BoujeeEnjinia1701/cellguard/cad/drawings/CGD-DWG-104.pdf

### BUILD PLAN SKETCH, PLAN NOT YET BUILT CellGuard · github.com/BoujeeEnjinia1701/cellguard

FRONT VIEW
Scale 1:2; looking at the front (along +Y)

TOP VIEW
Scale 1:2; looking down (along -Z)

RIGHT VIEW
Scale 1:2; looking at the right side (along -X)

134

104 26

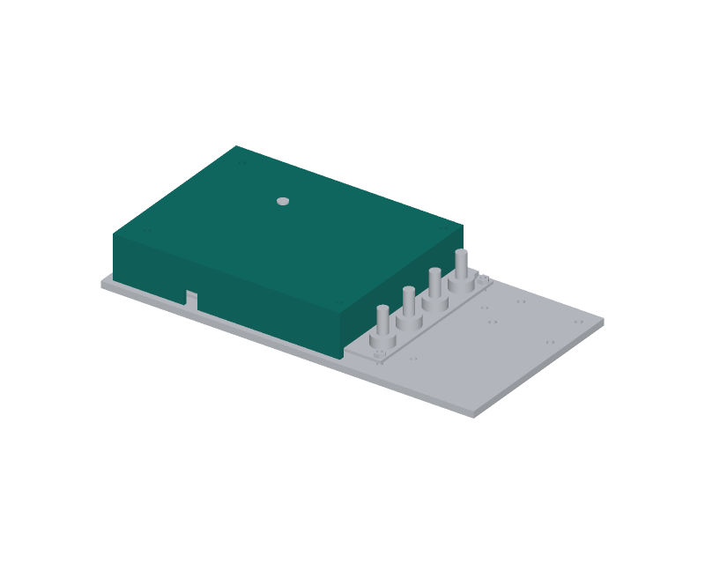
[picture p10: figure]

WHERE IT GOES
This part in colour, its neighbours in grey

HOW TO MAKE IT AND HOW IT FITS
Print upside down (top face on the bed), 2 mm walls, 100 % infill, in flame-retardant polycarbonate in an enclosed printer. Outside 134 x 104 x 26.1 mm, open at the bottom.
Four 3.4 mm holes in the top over the pillars: 12 mm from the signal end 40 each side, and 128 mm from it 44 each side. Signal-end notch 68 wide, from 26 below to 42 above the centre line, open at the bottom, 15.1 mm tall: the connectors and harness sit in it. Power-end notch 98 wide, 5.1 mm tall, open at the bottom: the board passes under it with 1 mm clear. Probe notch 8 wide, 9.1 mm tall, in the near side wall.
Light pipe hole 3.2 mm in the top, 50 mm from the signal end, 20 to the B+ side: press the flanged 3 mm light pipe in from above; its foot stops 0.5 mm over the status light.
Fit: it rests on the four pillars only; its walls stand 0.5 mm clear of the plate. Four M3 x 6 pan-head screws.
Check: on the pillars it does not rock and touches no part.
REV | DESCRIPTION | DATE | BY
P1 | Making sketch for the prototype build plan | 2026-09-30 | AC
P2 | Status light and light pipe added (CGD-DEC-001) | 2026-10-02 | AC
CELLGUARD | github.com/BoujeeEnjinia1701/cellguard

## CellGuard cover: making sketch

DRAWING NO.
CGD-DWG-104

REV
P2

SHEET
1 of 1

SIZE

## ANSI B

SCALE
1:2

UNITS
mm
PROJECTION | DATE
2026-10-02

DRAWN
Amish Chadha

MATERIAL / NOTES
Flame-retardant polycarbonate, opaque, printed, 2 mm wall
Licensed CERN-OHL-S-2.0 · Design Molecule Lab · designmolecule.com | Generated from cad/src; do not edit by hand
