BoujeeEnjinia1701/cellguard/cad/drawings/CGD-DWG-101.pdf

### BUILD PLAN SKETCH, PLAN NOT YET BUILT CellGuard · github.com/BoujeeEnjinia1701/cellguard

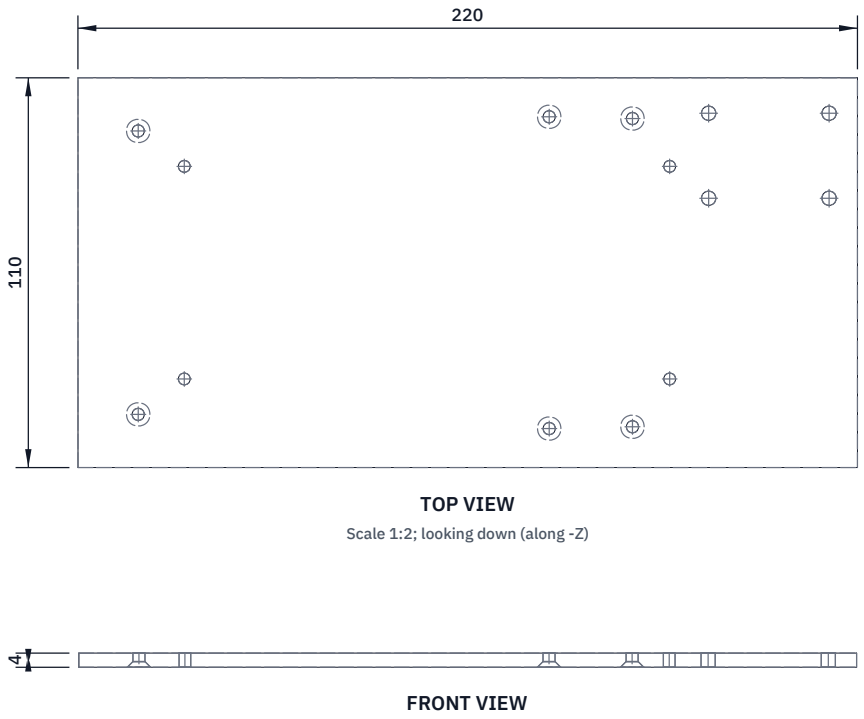
[picture p36: figure]
FRONT VIEW; TOP VIEW; Scale 1:2; looking down (along -Z)

Scale 1:2; looking at the front (along +Y)

RIGHT VIEW
Scale 1:2; looking at the right side (along -X)

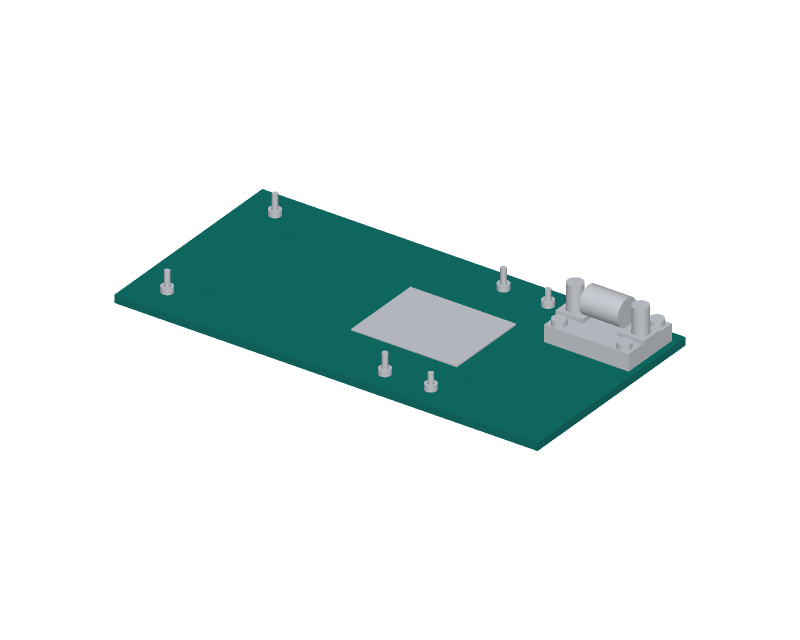
[picture p37: figure]

WHERE IT GOES
This part in colour, its neighbours in grey

HOW TO MAKE IT AND HOW IT FITS
Blank 220 x 110 mm, 4 mm aluminium, square; round the corners 3 mm. Sizes from the signal end (left edge) and the centre line.
Board fixings: six 3.4 mm holes, countersunk 90 degrees from
the BOTTOM face to 6.6 mm so M3 countersunk heads sit flush:
17 from the left edge 40 each side; 133 in, 44 each side;
156.5 in, 43.5 each side.
Fuse holder: four M4 tapped holes (drill 3.3) at 178 and 212 in, 21 and 45 to the B+ side of the centre line.
Mounting: four M4 tapped holes (drill 3.3) at 30 and 167 in,
30 each side. Screws come up from below and stop in the plate. Deburr every hole; the top face must stay flat within 0.1 mm under the gap pad (it carries the MOSFET heat).
Check: lay the board on it; all six holes line up with the board's.
REV | DESCRIPTION | DATE | BY
P1 | Making sketch for the prototype build plan | 2026-09-30 | AC
CELLGUARD | github.com/BoujeeEnjinia1701/cellguard

## CellGuard base plate: making sketch

DRAWING NO.
CGD-DWG-101

REV
P1

SHEET
1 of 1

SIZE

## ANSI B

SCALE
1:2

UNITS
mm
PROJECTION | DATE
2026-09-30

DRAWN
Amish Chadha

MATERIAL / NOTES
Aluminium sheet 4 mm, 6061 class
Licensed CERN-OHL-S-2.0 · Design Molecule Lab · designmolecule.com | Generated from cad/src; do not edit by hand
