BoujeeEnjinia1701/cellguard/cad/drawings/CGD-DWG-102.pdf

### BUILD PLAN SKETCH, PLAN NOT YET BUILT CellGuard · github.com/BoujeeEnjinia1701/cellguard

FRONT VIEW
Scale 2:1; looking at the front (along +Y)

TOP VIEW
Scale 2:1; looking down (along -Z)

RIGHT VIEW
Scale 2:1; looking at the right side (along -X)

55

44 1

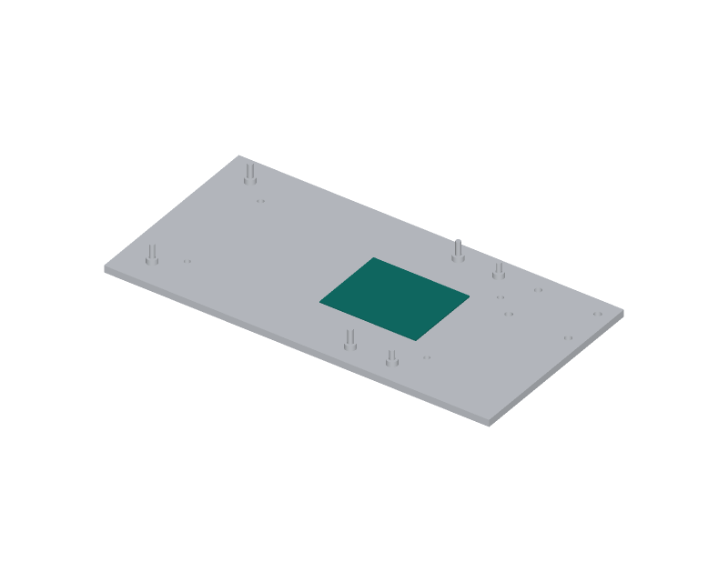
[picture p38: figure]

WHERE IT GOES
This part in colour, its neighbours in grey

HOW TO MAKE IT AND HOW IT FITS
Cut one piece 55 x 44 mm from 1.0 mm insulating gap pad sheet with a sharp knife on a cutting mat; keep the liner on.
Drawn at 0.7 mm: the thickness it is squeezed to in place.
It lies on the plate under the eight MOSFETs: from 100 to 155 mm in from the plate's left edge, centred across the plate.
Peel one liner, press it onto the clean plate, then peel the
other liner just before the board goes on.
Do not stretch it; replace it if it tears or picks up a chip:
it is the only insulation between the MOSFETs and the plate. Check: no bubbles; 55 x 44 mm within 1 mm.
REV | DESCRIPTION | DATE | BY
P1 | Making sketch for the prototype build plan | 2026-09-30 | AC
CELLGUARD | github.com/BoujeeEnjinia1701/cellguard

## CellGuard gap pad: cutting sketch

DRAWING NO.
CGD-DWG-102

REV
P1

SHEET
1 of 1

SIZE

## ANSI B

SCALE
2:1

UNITS
mm
PROJECTION | DATE
2026-09-30

DRAWN
Amish Chadha

MATERIAL / NOTES
Insulating gap pad 1.0 mm, 3 W/m.K
Licensed CERN-OHL-S-2.0 · Design Molecule Lab · designmolecule.com | Generated from cad/src; do not edit by hand
