BoujeeEnjinia1701/cellguard/cad/drawings/CGD-DWG-105.pdf

### BUILD PLAN SKETCH, PLAN NOT YET BUILT CellGuard · github.com/BoujeeEnjinia1701/cellguard

FRONT VIEW
Scale 2:1; looking at the front (along +Y)

TOP VIEW
Scale 2:1; looking down (along -Z)

RIGHT VIEW
Scale 2:1; looking at the right side (along -X)

41

14 3

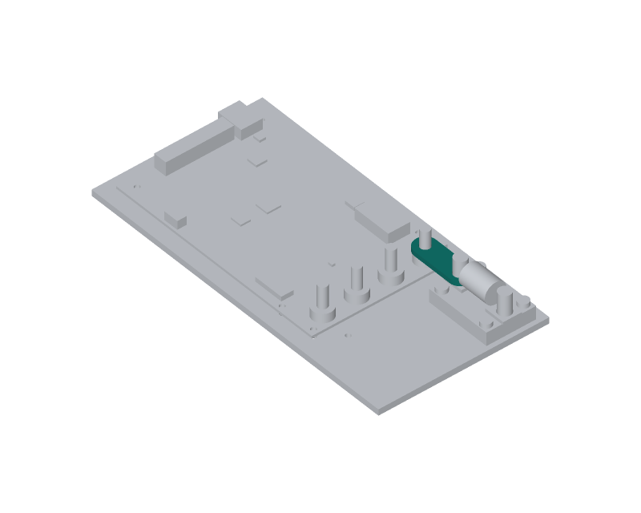
[picture p39: figure]

WHERE IT GOES
This part in colour, its neighbours in grey

HOW TO MAKE IT AND HOW IT FITS
Cut 41 mm of 14 x 3 mm copper bar; file both ends to a 7 mm radius, centred on the hole centres.
Holes on the centre line, 27 mm apart: 6.5 mm at one end (B+ stud, M6), 8.5 mm at the other (fuse holder terminal, M8). Deburr; clean both faces bright with an abrasive pad.
Slide 20 mm of heat-shrink over the middle and shrink it; leave the ends bare where they clamp.
Fit: lies flat on the B+ stud's shoulder and on the fuse blade
at the holder's inner terminal, both 10.6 mm above the plate top. An M6 and an M8 nut with spring washers hold it.
It carries the full pack current: both faces must be clean and flat where they touch.
Check: drops over both studs without bending.
REV | DESCRIPTION | DATE | BY
P1 | Making sketch for the prototype build plan | 2026-09-30 | AC
CELLGUARD | github.com/BoujeeEnjinia1701/cellguard

## CellGuard fuse link: making sketch

DRAWING NO.
CGD-DWG-105

REV
P1

SHEET
1 of 1

SIZE

## ANSI B

SCALE
2:1

UNITS
mm
PROJECTION | DATE
2026-09-30

DRAWN
Amish Chadha

MATERIAL / NOTES
Copper flat bar 14 x 3 mm, C101 or C110
Licensed CERN-OHL-S-2.0 · Design Molecule Lab · designmolecule.com | Generated from cad/src; do not edit by hand
