BoujeeEnjinia1701/cellguard/cad/drawings/CGD-DWG-001.png

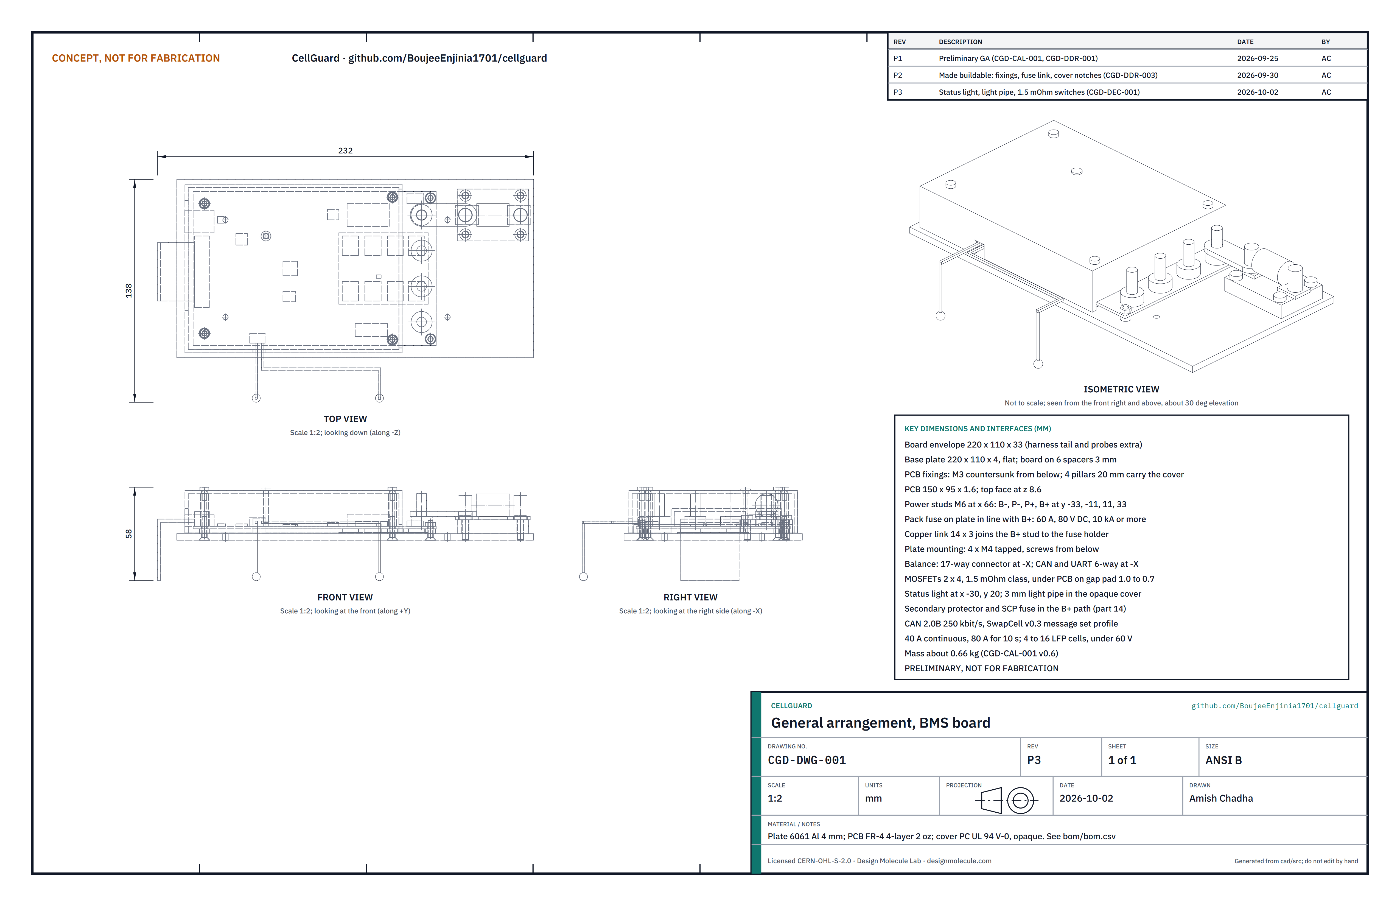
cad/drawings/CGD-DWG-001.png
