BoujeeEnjinia1701/cellguard/media/card.png

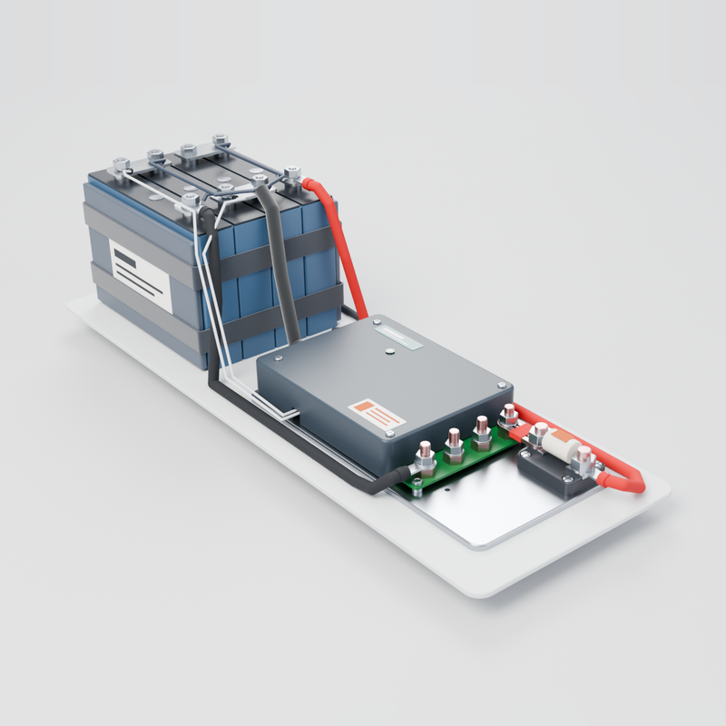
media/card.png
