BoujeeEnjinia1701/cellguard/media/render-detail.png

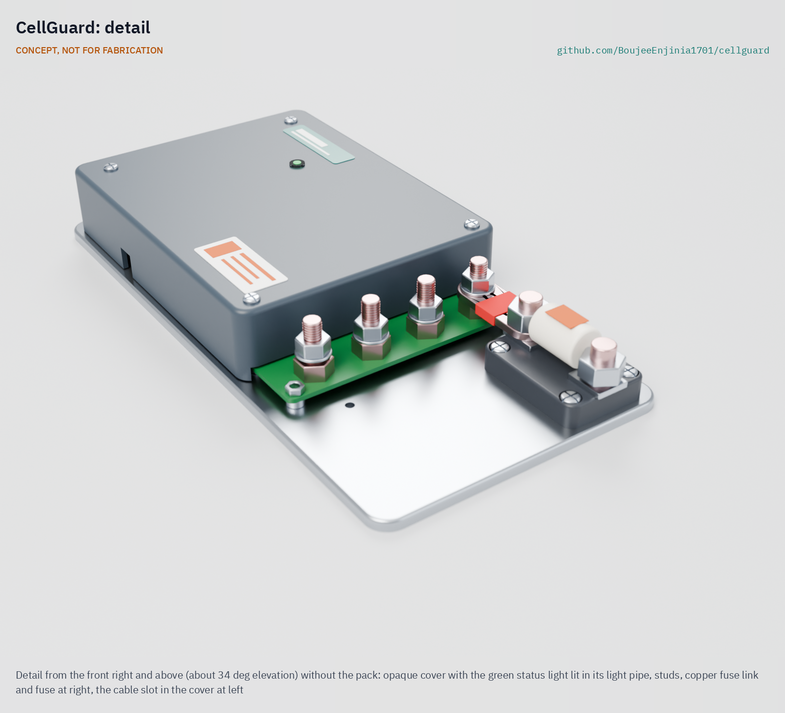
media/render-detail.png
