BoujeeEnjinia1701/cellguard/media/render-exploded.png

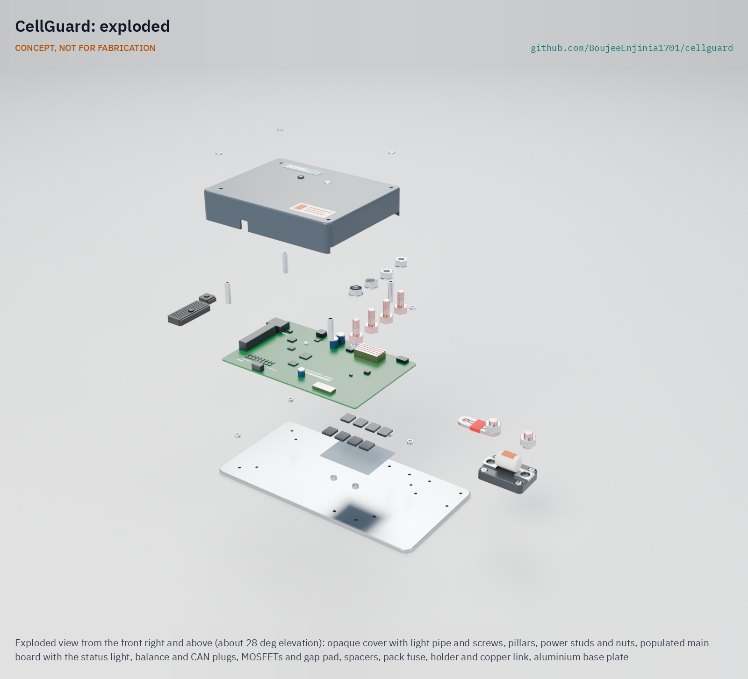
media/render-exploded.png
