BoujeeEnjinia1701/cellguard/media/social-preview.png

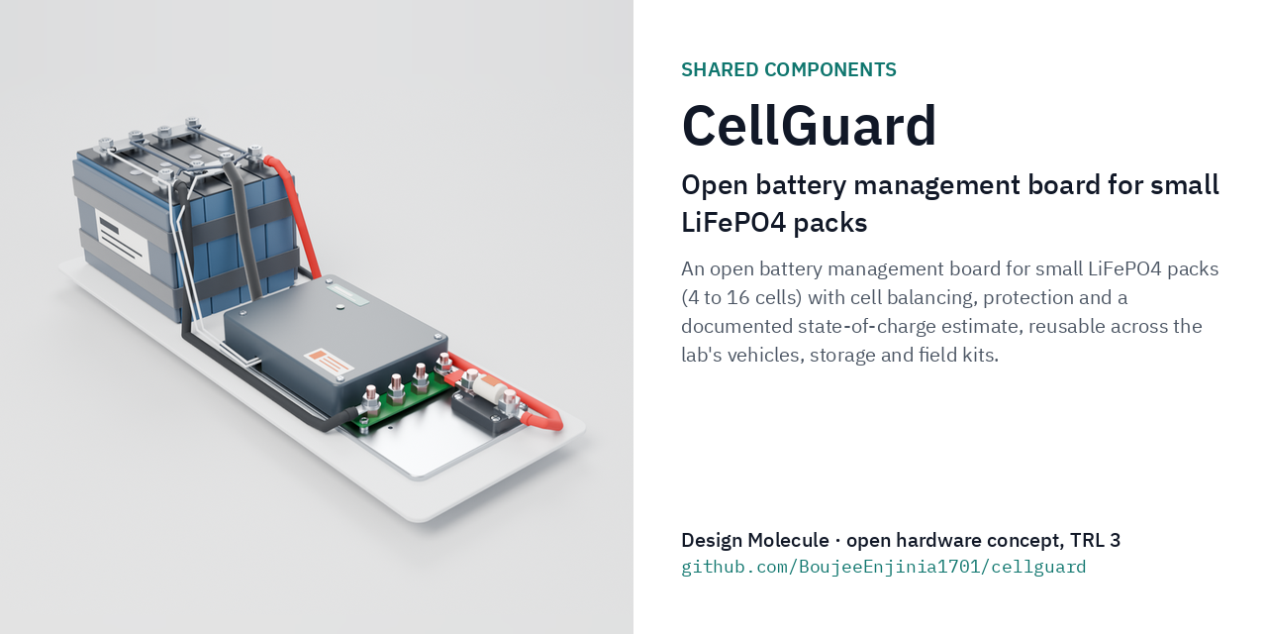
media/social-preview.png
